SSP-CDMX/hw-mpn-eth/Imagenes/SensorMagnetico.png

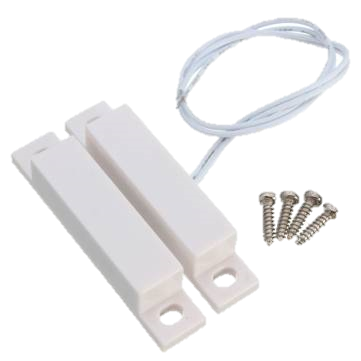
Imagenes/SensorMagnetico.png
